Breadstick-Innovations/22008-RP2040-Dev-Board/Photos/Rev 4/RP2040 Dev Board with Header Pins Blue Background Front - Small.JPG

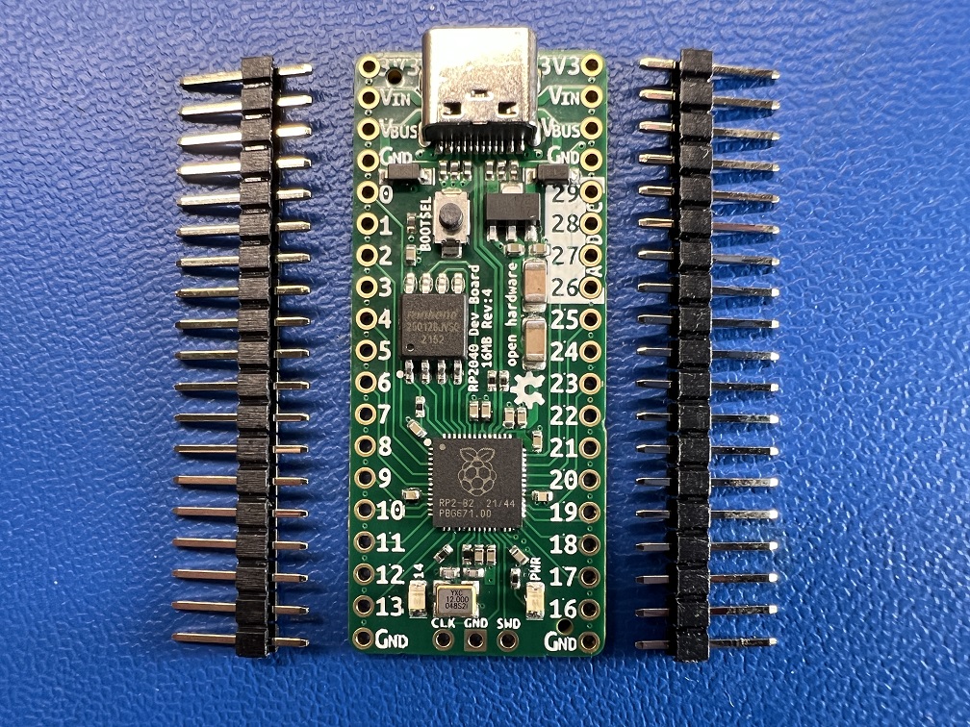
Photos/Rev 4/RP2040 Dev Board with Header Pins Blue Background Front - Small.JPG
