Breadstick-Innovations/22008-RP2040-Dev-Board/Photos/Rev 4/Tindie 3x2/Package & Cable.JPG

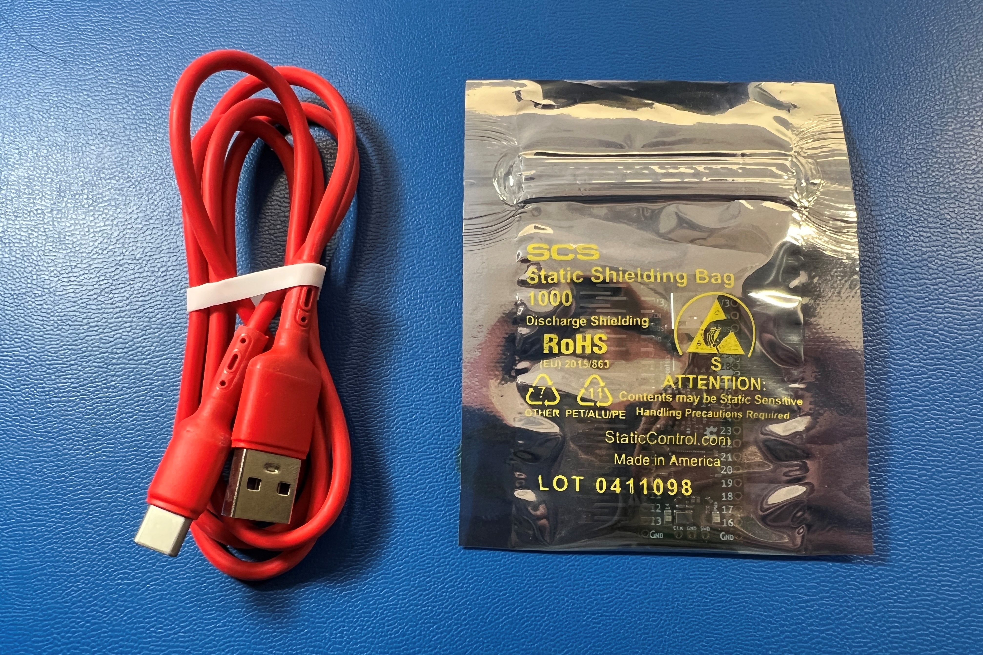
Photos/Rev 4/Tindie 3x2/Package & Cable.JPG
