Breadstick-Innovations/22008-RP2040-Dev-Board/Renders/Rev4/Board Dimensions.jpg

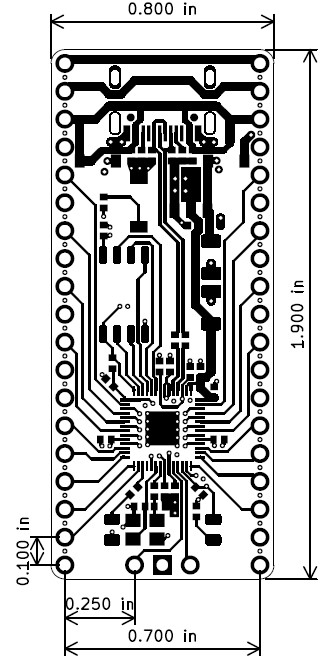
Renders/Rev4/Board Dimensions.jpg
