Breadstick-Innovations/22008-RP2040-Dev-Board/Renders/Rev4/RP2040 Dev Board Front Isometric White Background.png

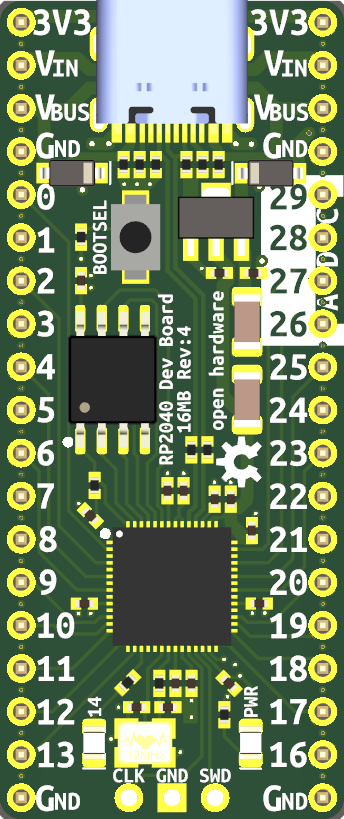
Renders/Rev4/RP2040 Dev Board Front Isometric White Background.png
